claudiofin/smartbag/media/evidence/artwork-all-layers.png

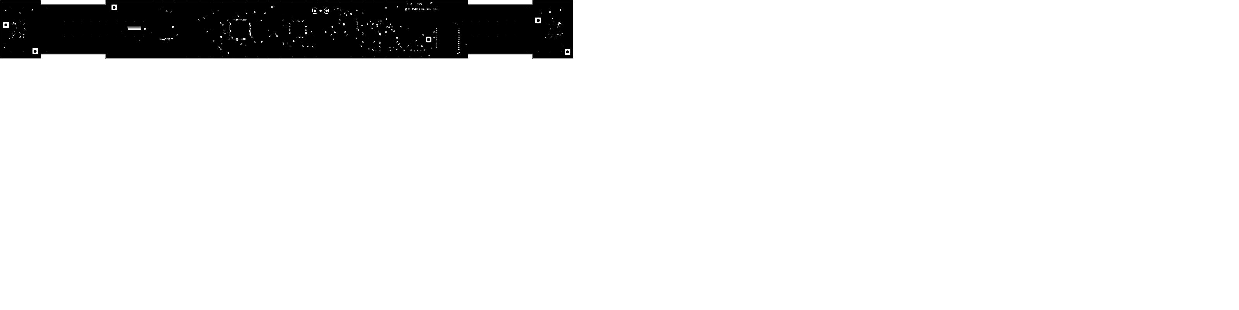
media/evidence/artwork-all-layers.png
