claudiofin/smartbag/render/views/app_mock.png

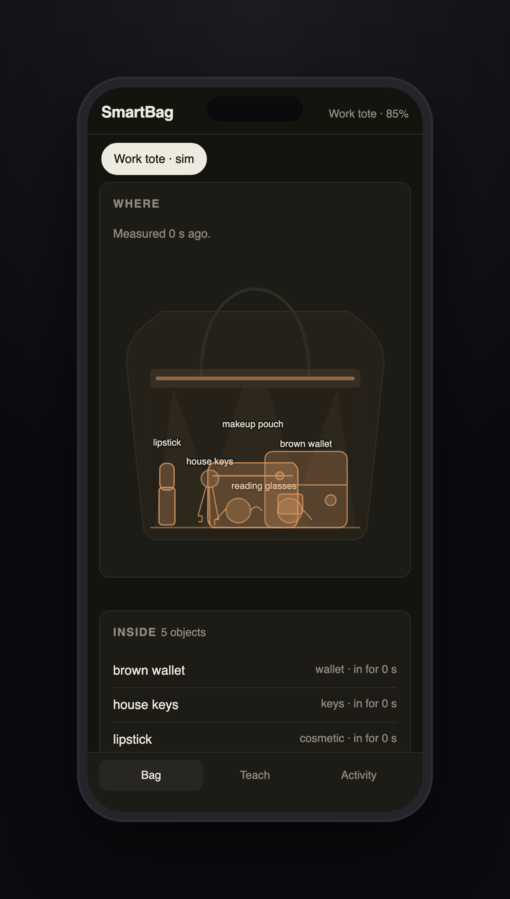
render/views/app_mock.png
