claudiofin/smartbag/render/views/press.png

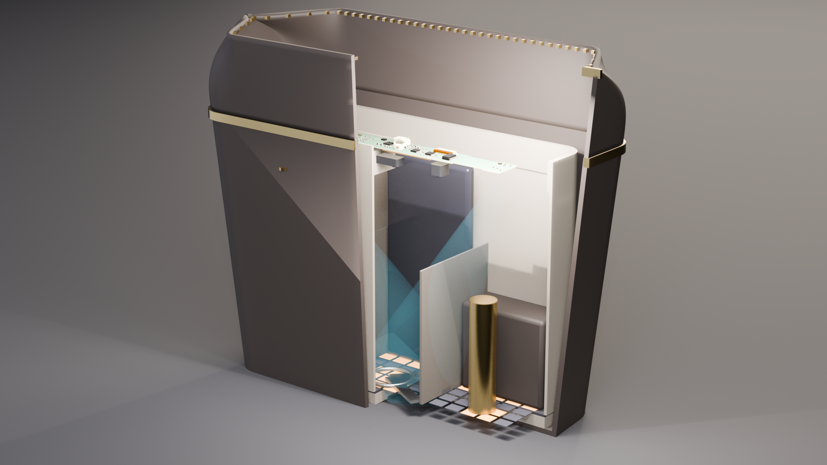
render/views/press.png
