claudiofin/smartbag/media/evidence/verification.png

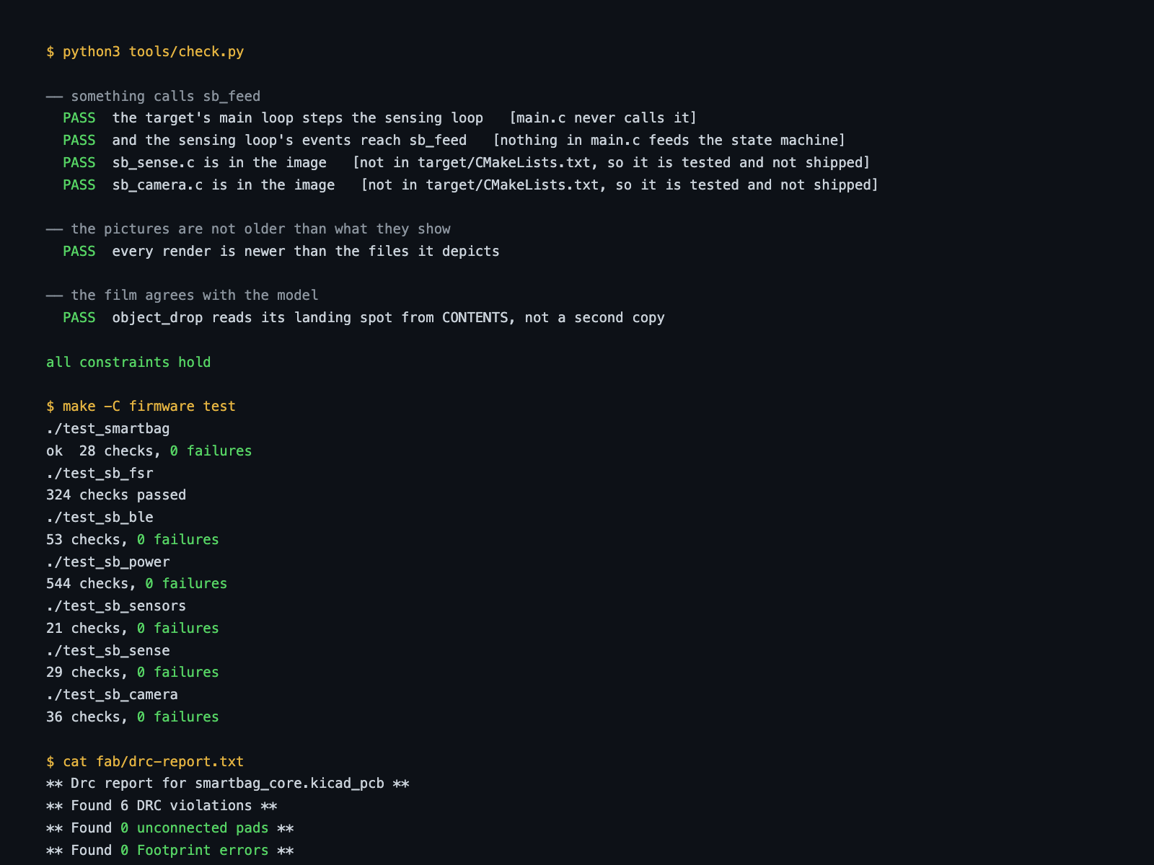
media/evidence/verification.png
